lohjo/hardware_projects/lifeline/sketches/blood_sampler.png

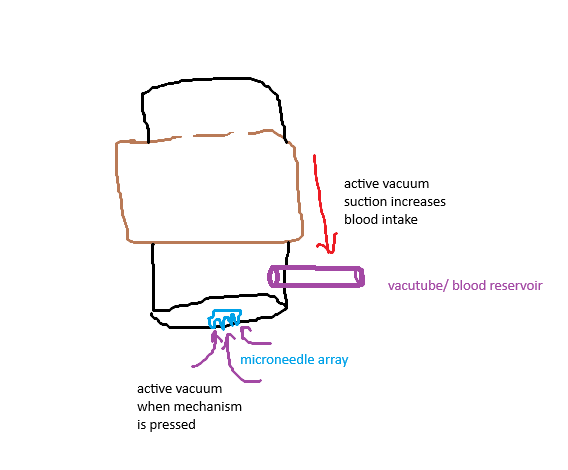
lifeline/sketches/blood_sampler.png
