lohjo/hardware_projects/lifeline/sketches/button_pen_mechanism.png

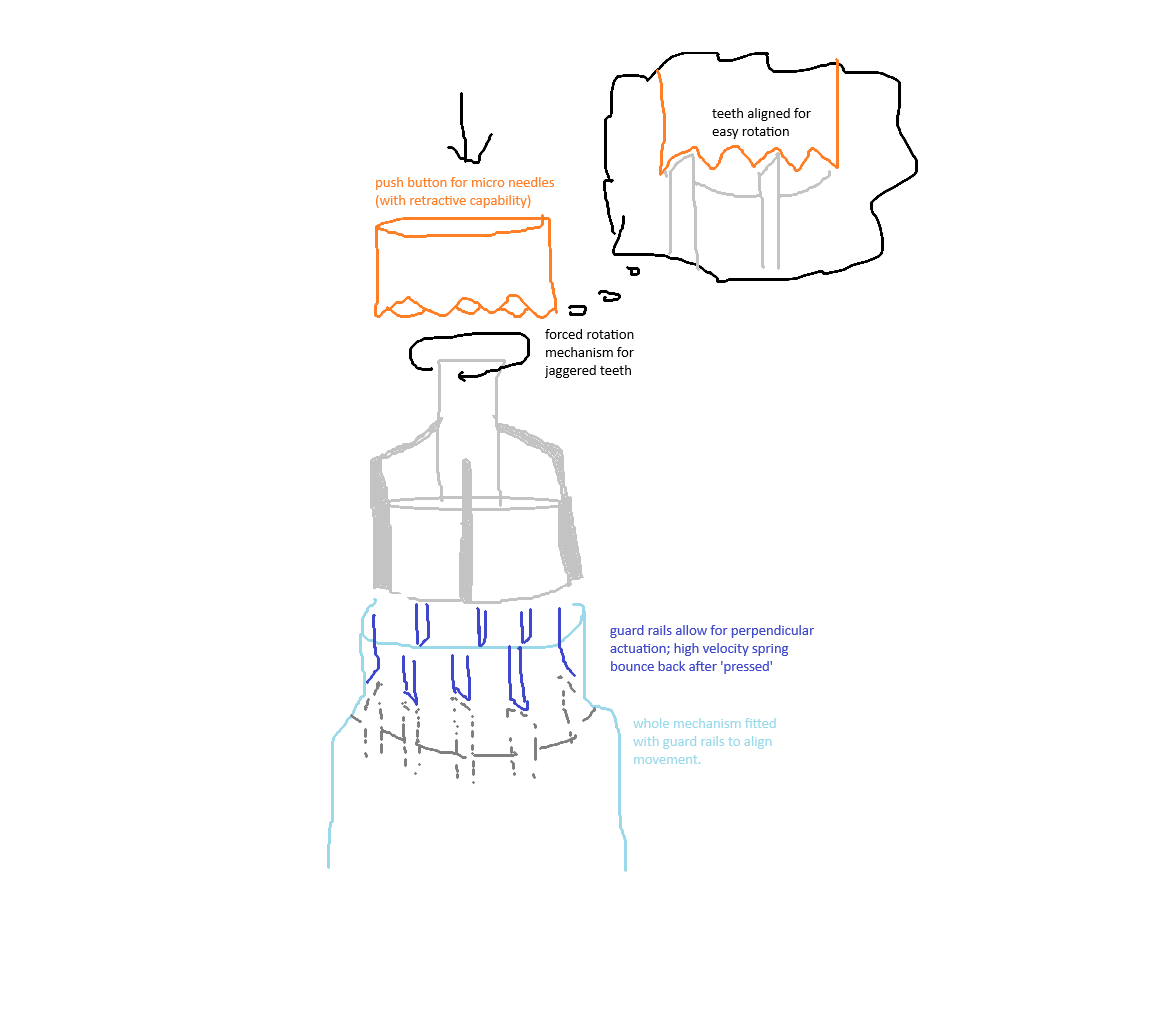
lifeline/sketches/button_pen_mechanism.png
