lohjo/hardware_projects/lifeline/sketches/Gemini_Generated_Image_1iue3b1iue3b1iue(1).png

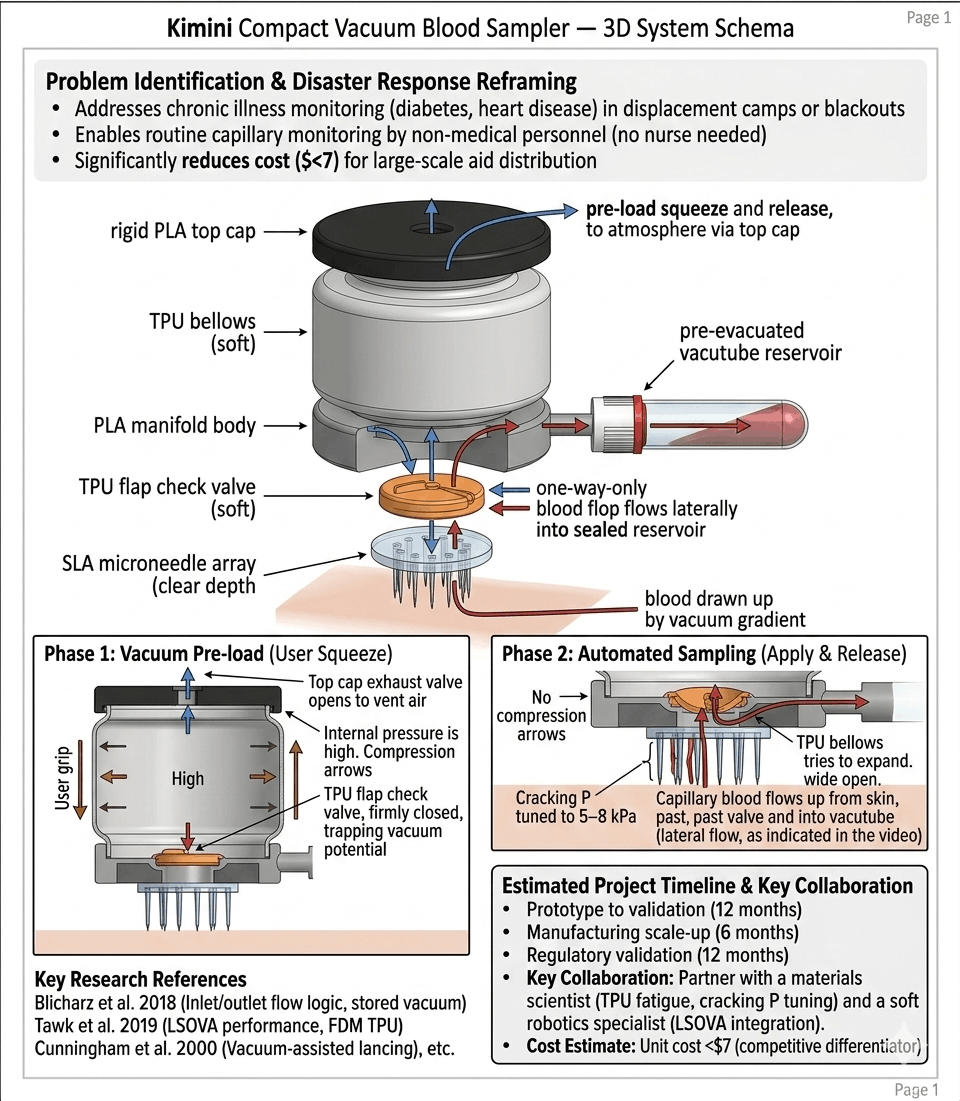
lifeline/sketches/Gemini_Generated_Image_1iue3b1iue3b1iue(1).png
