lohjo/hardware_projects/lifeline/sketches/Gemini_Generated_Image_1iue3b1iue3b1iue.png

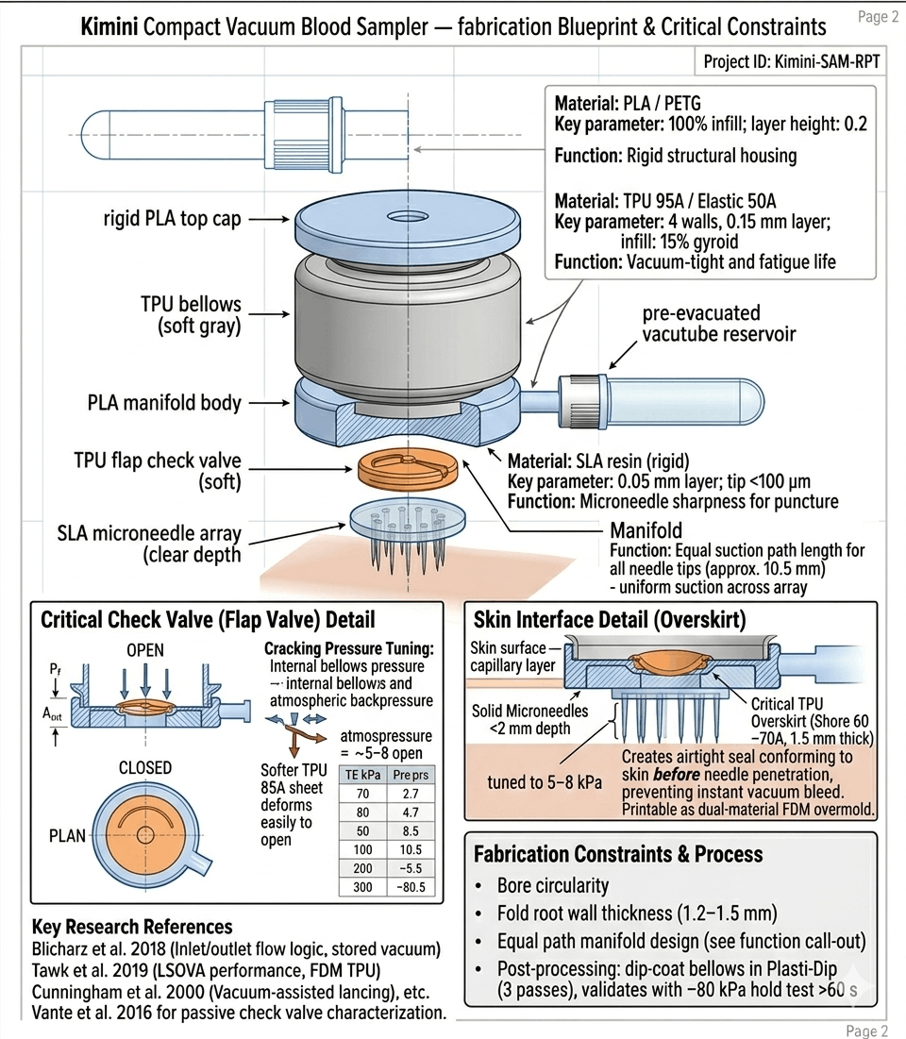
lifeline/sketches/Gemini_Generated_Image_1iue3b1iue3b1iue.png
