lohjo/hardware_projects/lifeline/sketches/Gemini_Generated_Image_nv72dpnv72dpnv72.png

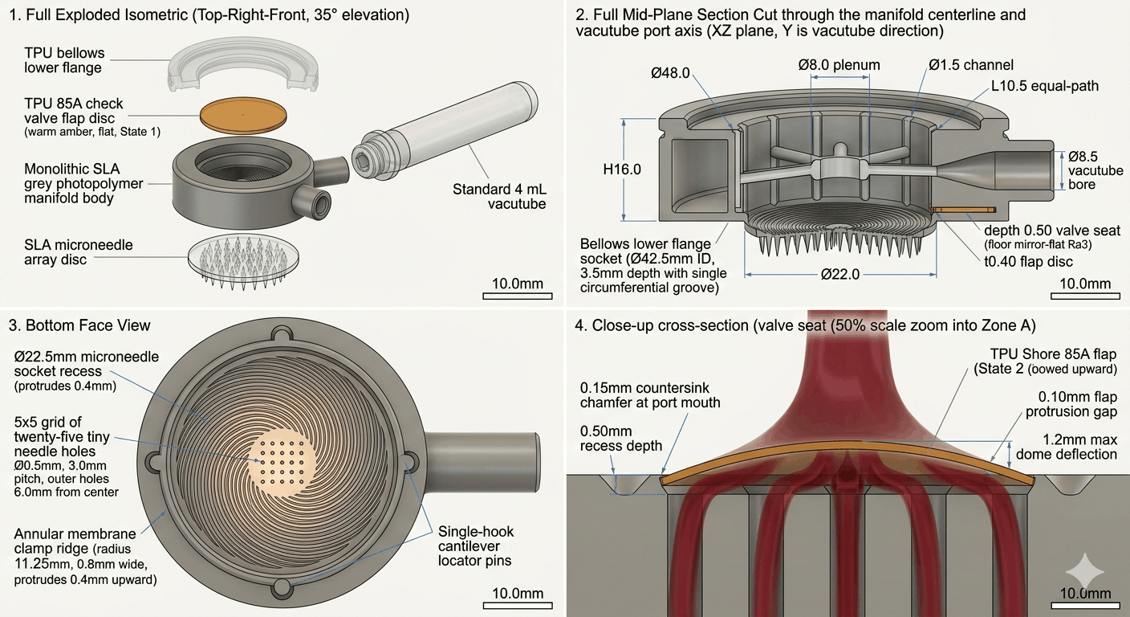
lifeline/sketches/Gemini_Generated_Image_nv72dpnv72dpnv72.png
