lohjo/hardware_projects/lifeline/sketches/image.png

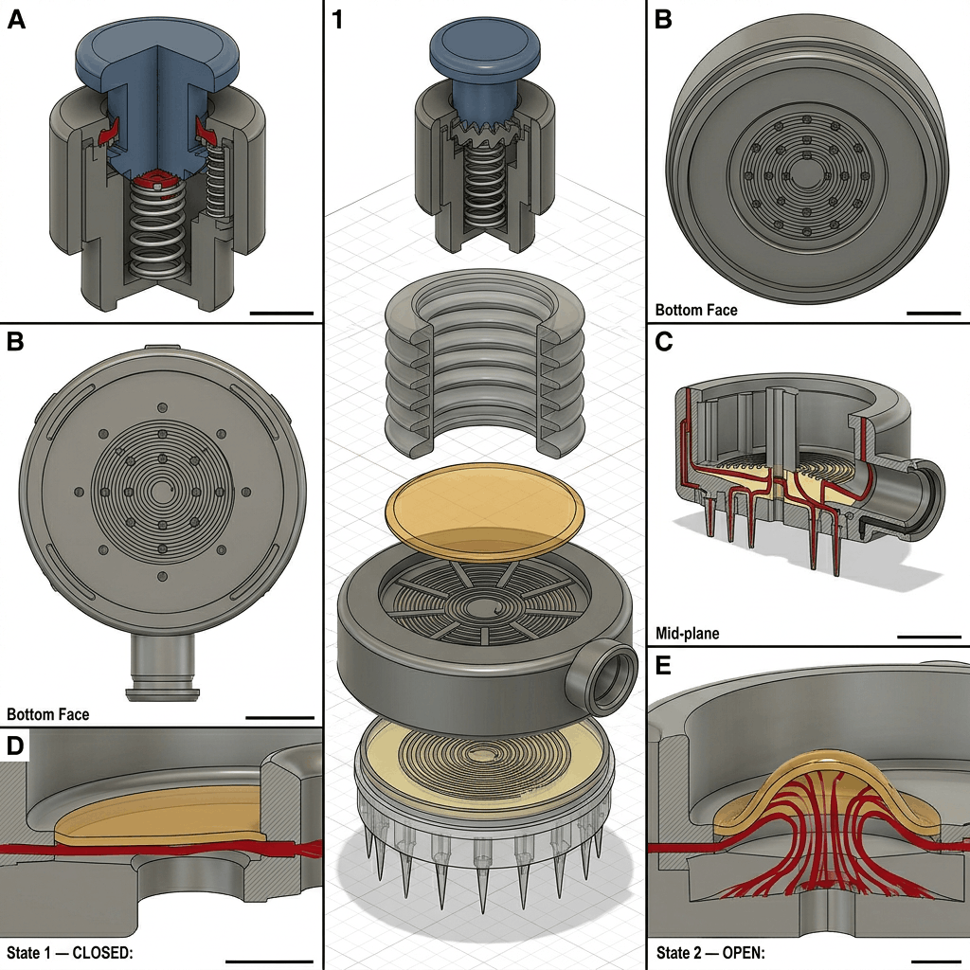
lifeline/sketches/image.png
