lohjo/hardware_projects/lifeline/src/renders/quickly_draw_002_top.png

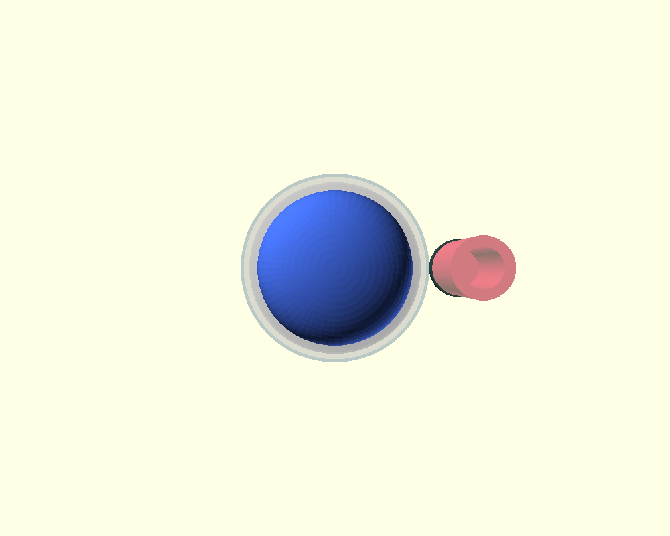
lifeline/src/renders/quickly_draw_002_top.png
