lohjo/hardware_projects/lifeline/uploads/Screenshot 2026-03-20 101646.png

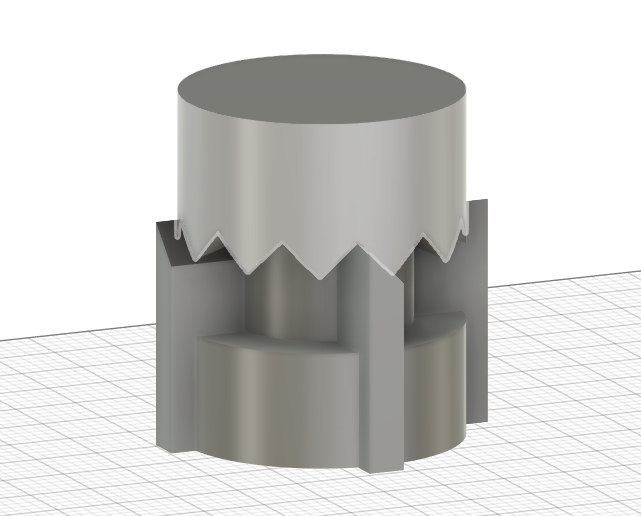
lifeline/uploads/Screenshot 2026-03-20 101646.png
